46nori/PicoLight/KiCad/PicoLight.kicad_sch

## KiCad design KiCad/PicoLight.kicad_sch (2024-04-15)

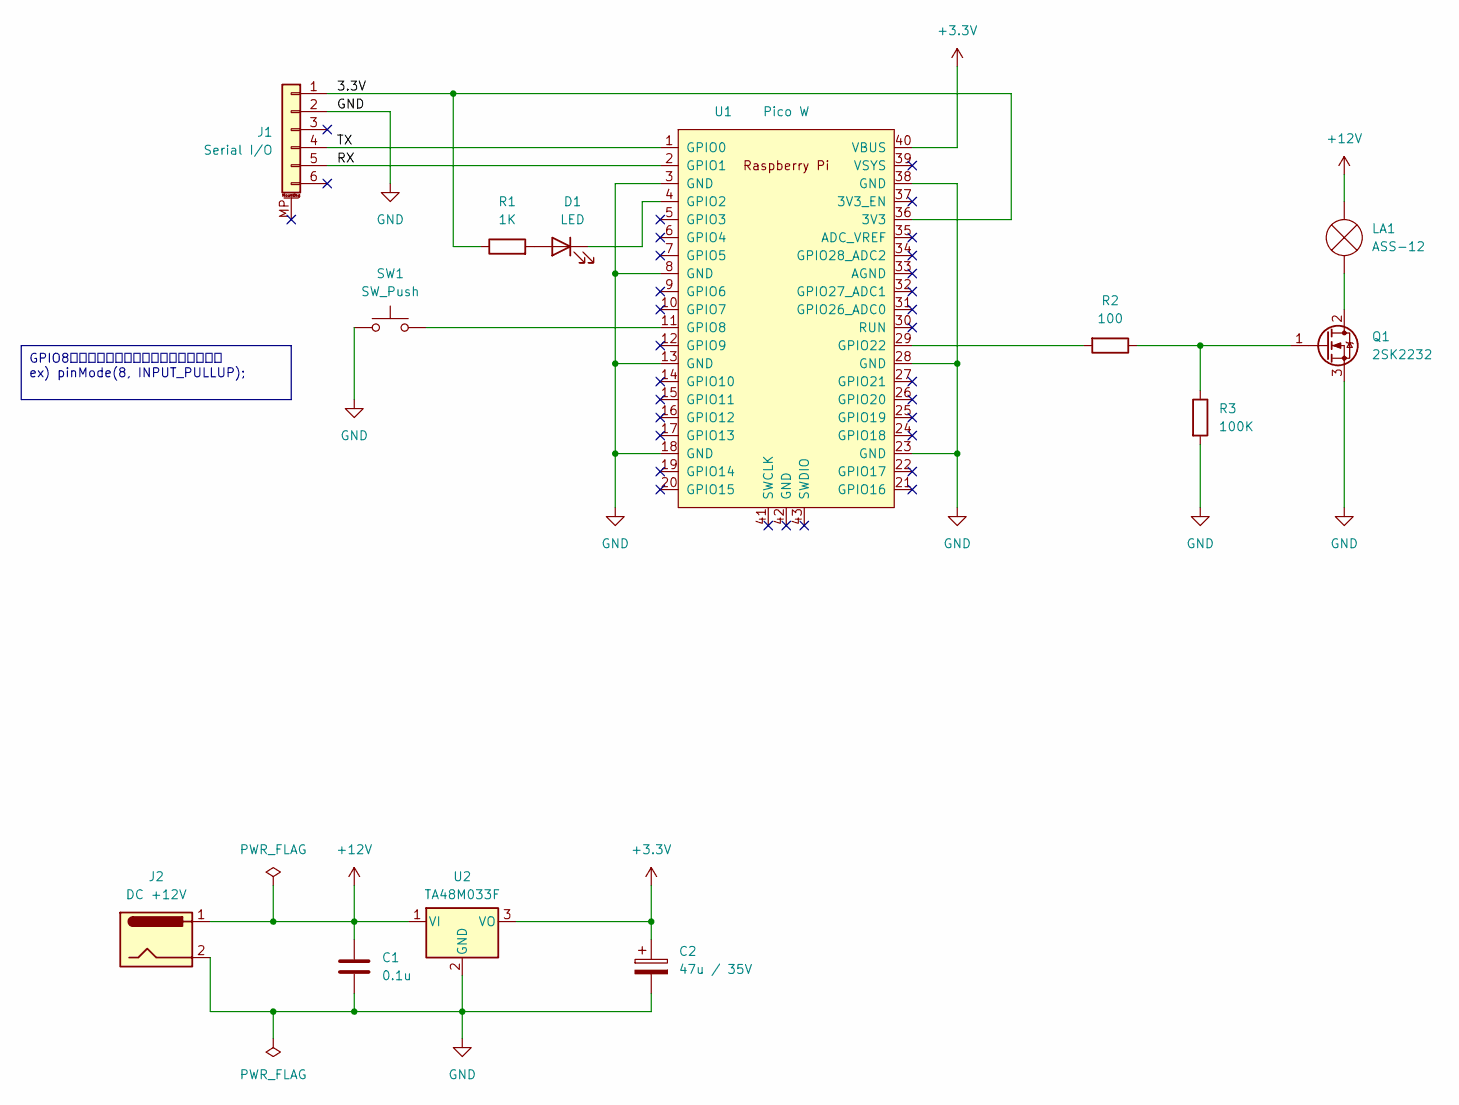
[picture p2: schematic PicoLight.kicad_sch]

Parts:
C1: 0.1u
C2: 47u / 35V
D1: LED
J1: Serial I/O
J2: DC +12V
LA1: ASS-12
Q1: 2SK2232
R1: 1K
R2: 100
R3: 100K
SW1: SW_Push
U1: Pico W; RPi_Pico_SMD_TH
U2: TA48M033F; TO-252-2

Connections:
3.3V: J1.1, R1.1, U1.36 (3V3)
+3.3V: C2.1, U1.40 (VBUS), U2.3 (VO)
+12V: C1.1, J2.1, LA1.2 (+), U2.1 (VI)
GND: C1.2, C2.2, J1.2, J2.2, Q1.3 (S), R3.2, SW1.1, U1.3 (GND), U1.8 (GND), U1.13 (GND), U1.18 (GND), U1.23 (GND), U1.28 (GND), U1.38 (GND), U2.2 (GND)
unnamed: D1.1 (K), U1.4 (GPIO2)
unnamed: D1.2 (A), R1.2
unnamed: LA1.1 (-), Q1.2 (D)
unnamed: Q1.1 (G), R2.1, R3.1
unnamed: R2.2, U1.29 (GPIO22)
unnamed: SW1.2, U1.11 (GPIO8)
RX: J1.5, U1.2 (GPIO1)
TX: J1.4, U1.1 (GPIO0)

Notes on the sheet:
GPIO8は内部プルアップの設定にすること。 ex) pinMode(8, INPUT_PULLUP);
